marqs85/cps2_digiav/sw_common/sys_controller/src/menu.c

//
// Copyright (C) 2020  Markus Hiienkari <mhiienka@niksula.hut.fi>
//
// This file is part of CPS2 Digital AV Interface project.
//
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

#include <string.h>
#include "sysconfig.h"
#include "menu.h"
#include "avconfig.h"
#include "osd_generator_regs.h"
#include "controls.h"
#include "userdata.h"

#define MAX_MENU_DEPTH 1

#define OPT_NOWRAP  0
#define OPT_WRAP    1

#ifdef OSDLANG_JP
#define LNG(e, j) j
#else
#define LNG(e, j) e
#endif

#define FW_VER      "0.94"

extern avconfig_t tc;
extern volatile osd_regs *osd;

char menu_row1[OSD_CHAR_COLS+1];
char menu_row2[OSD_CHAR_COLS+1];

uint8_t menu_active;

menunavi navi[MAX_MENU_DEPTH];
uint8_t navlvl;

static const char *off_on_desc[] = { LNG("Off","ｵﾌ"), LNG("On","ｵﾝ") };
static const char *ad_mode_id_desc[] = { "240p_CRT", "480p_CRT (Line2x)", "1280x720 (Line3x)", "1280x1024 (Line4x)", "1920x1080 (Line4x)", "1920x1080 (Line5x)", "1600x1200 (Line5x)", "1920x1200 (Line5x)", "1920x1440 (Line6x)" };
static const char *tx_mode_desc[] = { "HDMI (RGB Full)", "HDMI (RGB Limited)", "HDMI (YCbCr444)", "DVI" };
static const char *sl_mode_desc[] = { "Off", "Horizontal", "H+V" };
static const char *sl_method_desc[] = { "Multiplication", "Subtraction" };
static const char *audio_sr_desc[] = { "Off", "On (4.0)", "On (5.1)", "On (7.1)" };
static const char *neogeo_freq_desc[] = { "24MHz (MVS)", "24.167MHz (AES)", "24.306MHz (DFO)" };

static void value_disp(uint8_t v) { if (v < 10) {menu_row2[0] = ('0'+v); menu_row2[1] = 0;} else {menu_row2[0] = '0'+(v/10); menu_row2[1] = '0'+(v%10); menu_row2[2] = 0;} }


MENU(menu_main, P99_PROTECT({ \
    { "Output mode",                            OPT_AVCONFIG_SELECTION, { .sel = { &tc.ad_mode_id,              OPT_WRAP, SETTING_ITEM(ad_mode_id_desc) } } },
    { "1080p L5x Y-offset",                     OPT_AVCONFIG_NUMVALUE,  { .num = { &tc.l5x_1080p_y_offset,      OPT_WRAP, 0, L5X_1080P_YOFF_MAX, value_disp } } },
    { LNG("Scanlines","ｽｷｬﾝﾗｲﾝ"),                OPT_AVCONFIG_SELECTION, { .sel = { &tc.sl_mode,                OPT_WRAP,   SETTING_ITEM(sl_mode_desc) } } },
    { "Sl. method",                             OPT_AVCONFIG_SELECTION, { .sel = { &tc.sl_method,             OPT_WRAP,   SETTING_ITEM(sl_method_desc) } } },
    { LNG("Sl. strength","ｽｷｬﾝﾗｲﾝﾂﾖｻ"),          OPT_AVCONFIG_NUMVALUE,  { .num = { &tc.sl_str,                 OPT_WRAP, 0, SCANLINESTR_MAX, value_disp } } },
    { "HDR flag",                               OPT_AVCONFIG_SELECTION,  { .sel = { &tc.adv7513_cfg.hdr,      OPT_WRAP, SETTING_ITEM(off_on_desc) } } },
    { "VRR flag",                               OPT_AVCONFIG_SELECTION,  { .sel = { &tc.adv7513_cfg.vrr,      OPT_WRAP, SETTING_ITEM(off_on_desc) } } },
    { "Quad stereo",                            OPT_AVCONFIG_SELECTION,  { .sel = { &tc.adv7513_cfg.i2s_stereo_cfg, OPT_WRAP, SETTING_ITEM(audio_sr_desc) } } },
#ifdef NEOGEO
    { "XTAL freq",                             OPT_AVCONFIG_SELECTION,  { .sel = { &tc.neogeo_freq,            OPT_WRAP, SETTING_ITEM(neogeo_freq_desc) } } },
#endif
    { LNG("TX mode","TXﾓｰﾄﾞ"),                  OPT_AVCONFIG_SELECTION, { .sel = { &tc.adv7513_cfg.tx_mode,     OPT_WRAP, SETTING_ITEM(tx_mode_desc) } } },
    { "<Save settings>",                        OPT_FUNC_CALL,          { .fun = { save_settings, NULL } } },
    { LNG("<Reset settings>","<ｾｯﾃｲｵｼｮｷｶ    >"),  OPT_FUNC_CALL,          { .fun = { reset_target_avconfig, NULL } } },
    { "<Firmware info>",                        OPT_FUNC_CALL,          { .fun = { get_fw_info, NULL } } },
    { "<Exit menu>",                            OPT_FUNC_CALL,          { .fun = { exit_menu, NULL } } },
}))


int is_menu_active() {
    return !!menu_active;
}

void init_menu() {
    menu_active = 0;
    memset(navi, 0, sizeof(navi));
    navi[0].m = &menu_main;
    navlvl = 0;
}

int exit_menu() {
    menu_active = 0;
    osd->osd_config.menu_active = 0;

    return 0;
}

int save_settings() {
    return write_userdata(0);
}

int get_fw_info() {
    strncpy(menu_row2, "v" FW_VER " @ " __DATE__, OSD_CHAR_COLS);

    return 1;
}

void write_option_value(menuitem_t *item, int func_called, int retval)
{
    switch (item->type) {
        case OPT_AVCONFIG_SELECTION:
            strncpy(menu_row2, item->sel.setting_str[*(item->sel.data)], OSD_CHAR_COLS+1);
            break;
        case OPT_AVCONFIG_NUMVALUE:
            item->num.df(*(item->num.data));
            break;
        case OPT_FUNC_CALL:
            if (func_called) {
                if (retval <= 0)
                    strncpy(menu_row2, ((retval==0) ? "Done" : "Failed"), OSD_CHAR_COLS+1);
            } else if (item->fun.arg_info) {
                item->fun.arg_info->df(*item->fun.arg_info->data);
            } else {
                menu_row2[0] = 0;
            }
            break;
        default:
            break;
    }
}

void render_osd_page() {
    int i;
    menuitem_t *item;
    uint32_t row_mask[2] = {0, 0};

    for (i=0; i < navi[navlvl].m->num_items; i++) {
        item = &navi[navlvl].m->items[i];
        strncpy((char*)osd->osd_array.data[i][0], item->name, OSD_CHAR_COLS);
        row_mask[0] |= (1<<i);

        if ((item->type != OPT_SUBMENU) && (item->type != OPT_FUNC_CALL)) {
            write_option_value(item, 0, 0);
            strncpy((char*)osd->osd_array.data[i][1], menu_row2, OSD_CHAR_COLS);
            row_mask[1] |= (1<<i);
        }
    }

    osd->osd_sec_enable[0].mask = row_mask[0];
    osd->osd_sec_enable[1].mask = row_mask[1];
}

void display_menu(menucode_id code)
{
    menuitem_t *item;
    uint8_t *val, val_wrap, val_min, val_max;
    uint16_t *val_u16, val_u16_min, val_u16_max;
    int i, func_called = 0, retval = 0;

    item = &navi[navlvl].m->items[navi[navlvl].mp];

    // Parse menu control
    switch (code) {
    case SHOW_MENU:
        menu_active = 1;
        render_osd_page();
        osd->osd_config.menu_active = 1;
        break;
    case NEXT_OPT:
        if (item->type == OPT_FUNC_CALL)
            osd->osd_sec_enable[1].mask &= ~(1<<navi[navlvl].mp);
        navi[navlvl].mp = (navi[navlvl].mp+1) % navi[navlvl].m->num_items;
        break;
    case VAL_PLUS:
        switch (item->type) {
            case OPT_AVCONFIG_SELECTION:
            case OPT_AVCONFIG_NUMVALUE:
                val = item->sel.data;
                val_wrap = item->sel.wrap_cfg;
                val_min = item->sel.min;
                val_max = item->sel.max;
                *val = (*val < val_max) ? (*val+1) : (val_wrap ? val_min : val_max);
                break;
            case OPT_FUNC_CALL:
                retval = item->fun.f();
                func_called = 1;
                break;
            default:
                break;
        }
        break;
    default:
        break;
    }

    // Generate menu text
    item = &navi[navlvl].m->items[navi[navlvl].mp];
    strncpy(menu_row1, item->name, OSD_CHAR_COLS+1);
    write_option_value(item, func_called, retval);
    strncpy((char*)osd->osd_array.data[navi[navlvl].mp][1], menu_row2, OSD_CHAR_COLS);
    osd->osd_row_color.mask = (1<<navi[navlvl].mp);
    if (func_called || ((item->type == OPT_FUNC_CALL) && item->fun.arg_info != NULL))
        osd->osd_sec_enable[1].mask |= (1<<navi[navlvl].mp);
}
