marqs85/cps2_digiav/board/cps2/rtl/i2s_upsampler_2x.v

//
// Copyright (C) 2016-2017  Markus Hiienkari <mhiienka@niksula.hut.fi>
//
// This file is part of CPS2_digiav project.
//
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

`define I2S_CLK_GATING
`define DEBUG

module i2s_upsampler_2x (
    input reset_n,
    input I2S_BCK,
    input I2S_WS,
    input I2S_DATA,
    output I2S_BCK_out,
    output reg I2S_WS_out,
    output reg I2S_DATA_out,
    output reg [7:0] clkcnt_out
);

reg I2S_WS_2x;
reg I2S_DATA_2x;

reg I2S_WS_prev;
reg [2:0] sample_idx;
reg [2:0] resample_idx;

// Synchronizer regs
reg [2:0] sample_idx_L;
reg [2:0] sample_idx_LL;

// sample FIFO and pointers
reg [15:0] samplebuf_l[0:3];
reg [15:0] samplebuf_r[0:3];
reg [4:0] samplebuf_l_ctr;
reg [4:0] samplebuf_r_ctr;

reg [9:0] sample2x_ctr;
reg [4:0] resample_l_ctr;
reg [4:0] resample_r_ctr;

reg [7:0] clkcnt;
reg [5:0] clken_ctr;
reg clken;

`ifdef DEBUG
reg [7:0] bck_ctr;
reg [6:0] frame_ctr;

reg dbg_len_exp /* synthesis noprune */;
reg dbg_frame_exp /* synthesis noprune */;

reg dbg_fifo_ovf /* synthesis noprune */;
reg dbg_fifo_unf /* synthesis noprune */;
`endif

wire I2S_BCK_proc;

// I2S_BCK_out = (4/5)*I2S_BCK = 4MHz
pll_i2s pll_i2s_inst (
    .inclk0(I2S_BCK),
    .c0(I2S_BCK_proc),
    .locked()
);


// Record 16-bit samples at their native rate on the FIFO.
// Nominal CPS2 WS timing: 208 BCK cycles (31/32 frames), 192 BCK cycles (1/32 frames) -> avg: 207.5 BCK cycles.
// However, jitter in WS timing may occur due to e.g. insufficient PSU (check dbg_len_exp in SignalTap).
always @(posedge I2S_BCK or negedge reset_n)
begin
    if (!reset_n) begin
        samplebuf_l_ctr <= 0;
        samplebuf_r_ctr <= 0;
        I2S_WS_prev <= 0;
        sample_idx <= 0;
        clkcnt <= 0;
    end else begin
        if ((I2S_WS_prev == 1'b1) && (I2S_WS == 1'b0)) begin
            samplebuf_l_ctr <= 16;
            clkcnt_out <= clkcnt;
            sample_idx <= sample_idx + 1'b1;
        end else if ((I2S_WS_prev == 1'b0) && (I2S_WS == 1'b1)) begin
            samplebuf_r_ctr <= 16;
        end

        if (samplebuf_l_ctr > 0) begin
            samplebuf_l[sample_idx][samplebuf_l_ctr-1] <= I2S_DATA;
            samplebuf_l_ctr <= samplebuf_l_ctr - 1;
        end

        if (samplebuf_r_ctr > 0) begin
            samplebuf_r[sample_idx][samplebuf_r_ctr-1] <= I2S_DATA;
            samplebuf_r_ctr <= samplebuf_r_ctr - 1;
        end

        if ((I2S_WS_prev == 1'b1) && (I2S_WS == 1'b0))
            clkcnt <= 0;
        else
            clkcnt <= clkcnt + 1'b1;

        I2S_WS_prev <= I2S_WS;

`ifdef DEBUG
        if ((I2S_WS_prev == 1'b1) && (I2S_WS == 1'b0)) begin
            if (bck_ctr == 207) begin
                frame_ctr <= frame_ctr + 1;
            end else if (bck_ctr == 191) begin
                if (frame_ctr != 31)
                    dbg_frame_exp <= 1;

                frame_ctr <= 0;
            end else begin
                dbg_len_exp <= 1;
                if (bck_ctr < 200)
                    frame_ctr <= 0;
                else
                    frame_ctr <= frame_ctr + 1;
            end
            
            bck_ctr <= 0;
        end else begin
            bck_ctr <= bck_ctr + 1;
            dbg_len_exp <= 0;
            dbg_frame_exp <= 0;
        end
`endif
    end
end

initial begin
    resample_idx = 3'd4;
end

// Output samples at 2x rate (~48kHz), 83 o_BCK cycles per o_WS cycle.
always @(posedge I2S_BCK_proc or negedge reset_n)
begin
    reg [3:0] sample_idx_norm;

    if (!reset_n) begin
        sample2x_ctr <= 0;
        resample_l_ctr <= 0;
        resample_r_ctr <= 0;
        resample_idx <= 3'd4;
        clken_ctr <= 0;
    end else begin
        if ((sample2x_ctr == 0) || (sample2x_ctr == 83)) begin
            I2S_WS_2x <= 1'b0;
            resample_l_ctr <= 16;
            clken_ctr <= 32;
        end else if ((sample2x_ctr == 42) || (sample2x_ctr == (42+83))) begin
            I2S_WS_2x <= 1'b1;
            resample_r_ctr <= 16;
            clken_ctr <= 32;
        end else begin
            if (clken_ctr > 0)
                clken_ctr <= clken_ctr - 1'b1;
        end

        if (sample_idx_LL < resample_idx)
            sample_idx_norm = 4'd8 + sample_idx_LL;
        else
            sample_idx_norm = sample_idx_LL;

        if (sample2x_ctr == (83*2-1)) begin
            sample2x_ctr <= 0;

            // Check if FIFO is going to over/underflow
            if (sample_idx_norm > resample_idx + 4'd6) begin
                resample_idx <= resample_idx + 3;
`ifdef DEBUG
                dbg_fifo_unf <= 1'b1;
`endif
            end else if (sample_idx_norm < resample_idx + 4'd2) begin
                resample_idx <= resample_idx - 1;
`ifdef DEBUG
                dbg_fifo_ovf <= 1'b1;
`endif
            end else begin
                resample_idx <= resample_idx + 1'b1;
`ifdef DEBUG
                dbg_fifo_ovf <= 0;
                dbg_fifo_unf <= 0;
`endif
            end
        end else begin
            sample2x_ctr <= sample2x_ctr + 1'b1;
        end

        if (resample_l_ctr > 0) begin
            I2S_DATA_2x <= samplebuf_l[resample_idx][resample_l_ctr-1];
            resample_l_ctr <= resample_l_ctr - 1;
        end else if (resample_r_ctr > 0) begin
            I2S_DATA_2x <= samplebuf_r[resample_idx][resample_r_ctr-1];
            resample_r_ctr <= resample_r_ctr - 1;
        end

        sample_idx_L <= sample_idx;
        sample_idx_LL <= sample_idx_L;
    end
end

// launch outputs ar negative edge
always @(negedge I2S_BCK_proc)
begin
    I2S_WS_out <= I2S_WS_2x;
    I2S_DATA_out <= I2S_DATA_2x;
end

`ifdef I2S_CLK_GATING
always @(negedge I2S_BCK_proc)
begin
    clken <= (clken_ctr > 0) ? 1'b1 : 1'b0;
end

assign I2S_BCK_out = (I2S_BCK_proc & clken);
`else
assign I2S_BCK_out = I2S_BCK_proc;
`endif

endmodule
