marqs85/cps2_digiav/sw_common/sys_controller/inc/video_modes.h

//
// Copyright (C) 2020  Markus Hiienkari <mhiienka@niksula.hut.fi>
//
// This file is part of CPS2 Digital AV Interface project.
//
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

#ifndef VIDEO_MODES_H_
#define VIDEO_MODES_H_

#include <stdint.h>
#include "si5351.h"
#include "adv7513.h"

typedef enum {
    CRTMODE_240p      = 0,
    STDMODE_240p      = 1,
    CRTMODE_480p      = 2,
    STDMODE_480p      = 3,
    STDMODE_720p      = 5,
    STDMODE_1280x960  = 6,
    STDMODE_1280x1024 = 7,
    STDMODE_1080p     = 8,
    STDMODE_1600x1200 = 9,
    STDMODE_1920x1200 = 10,
    STDMODE_1920x1440 = 11
} mode_idx_t;

typedef enum {
    ADMODE_240p_CRT  = 0,
    ADMODE_480p_CRT  = 1,
    ADMODE_720p      = 2,
    ADMODE_1280x1024 = 3,
    ADMODE_1080p_4X  = 4,
    ADMODE_1080p_5X  = 5,
    ADMODE_1600x1200 = 6,
    ADMODE_1920x1200 = 7,
    ADMODE_1920x1440 = 8,
    ADMODE_LAST      = 8
} ad_mode_id_t;

typedef struct {
    uint16_t h_active;
    uint16_t v_active;
    uint16_t h_total;
    uint8_t  h_total_adj:5;
    uint16_t v_total:11;
    uint16_t h_backporch:9;
    uint16_t v_backporch:9;
    uint16_t h_synclen:9;
    uint8_t v_synclen:5;
} __attribute__((packed)) sync_timings_t;

typedef struct {
    uint32_t c1_hz;
    uint32_t vclks_per_frame;
    sync_timings_t timings;
    si5351_ms_config_t vclk_to_mclk_conf;
} source_params_t;

typedef struct {
    char name[10];
    HDMI_vic_t vic:8;
    sync_timings_t timings;
    HDMI_pixelrep_t tx_pixelrep:2;
    HDMI_pixelrep_t hdmitx_pixr_ifr:2;
    // for generated target mode
    uint8_t si_pclk_mult:4;
    si5351_ms_config_t si_ms_conf;
} mode_data_t;

typedef struct {
    ad_mode_id_t id;
    const source_params_t *src_params;
    uint8_t x_rpt;
    uint8_t y_rpt;
    int16_t x_offset_i;
    int16_t y_offset_i;
    si5351_ms_config_t si_ms_conf;
} ad_mode_data_t;

typedef struct {
    uint8_t x_rpt;
    uint8_t y_rpt;
    uint8_t x_skip;
    int16_t x_offset;
    int16_t y_offset;
    uint16_t x_size;
    uint16_t y_size;
    uint16_t framesync_line;
    uint8_t x_start_lb;
    int8_t y_start_lb;
} vm_mult_config_t;

typedef struct {
    uint16_t h_active;
    uint16_t v_active;
    uint32_t vclks_per_frame;
} input_mode_t;


void set_default_vm_table();

void step_ad_mode(uint8_t next);

uint32_t estimate_dotclk(mode_data_t *vm_in, uint32_t h_hz);

const ad_mode_data_t* get_output_mode(input_mode_t *im, ad_mode_id_t ad_mode_id, vm_mult_config_t *vm_conf, mode_data_t *vm_in, mode_data_t *vm_out);

#endif /* VIDEO_MODES_H_ */
