marqs85/cps2_digiav/sw_common/sys_controller/inc/menu.h

//
// Copyright (C) 2020  Markus Hiienkari <mhiienka@niksula.hut.fi>
//
// This file is part of CPS2 Digital AV Interface project.
//
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

#ifndef MENU_H_
#define MENU_H_

#include <stdint.h>

typedef enum {
    OPT_AVCONFIG_SELECTION,
    OPT_AVCONFIG_NUMVALUE,
    OPT_AVCONFIG_NUMVAL_U16,
    OPT_SUBMENU,
    OPT_FUNC_CALL,
} menuitem_type;

typedef int (*func_call)(void);
typedef void (*arg_func)(void);
typedef void (*disp_func)(uint8_t);
typedef void (*disp_func_u16)(uint16_t*);

typedef struct {
    uint8_t *data;
    uint8_t max;
    disp_func df;
} arg_info_t;

typedef struct {
    uint8_t *data;
    uint8_t wrap_cfg;
    uint8_t min;
    uint8_t max;
    const char **setting_str;
} opt_avconfig_selection;

typedef struct {
    uint8_t *data;
    uint8_t wrap_cfg;
    uint8_t min;
    uint8_t max;
    disp_func df;
} opt_avconfig_numvalue;

typedef struct {
    uint16_t *data;
    uint16_t min;
    uint16_t max;
    disp_func_u16 df;
} opt_avconfig_numvalue_u16;

typedef struct {
    func_call f;
    const arg_info_t *arg_info;
} opt_func_call;

typedef struct menustruct menu_t;

typedef struct {
    const menu_t *menu;
    const arg_info_t *arg_info;
    arg_func arg_f;
} opt_submenu;

typedef struct {
    const char *name;
    menuitem_type type;
    union {
        opt_avconfig_selection sel;
        opt_avconfig_numvalue num;
        opt_avconfig_numvalue_u16 num_u16;
        opt_submenu sub;
        opt_func_call fun;
    };
} menuitem_t;

struct menustruct {
    uint8_t num_items;
    menuitem_t *items;
};

#define SETTING_ITEM(x) 0, sizeof(x)/sizeof(char*)-1, x
#define MENU(X, Y) menuitem_t X##_items[] = Y; const menu_t X = { sizeof(X##_items)/sizeof(menuitem_t), X##_items };
#define P99_PROTECT(...) __VA_ARGS__

typedef enum {
    SHOW_MENU    = 0,
    NEXT_OPT,
    VAL_PLUS
} menucode_id;

typedef struct {
    const menu_t *m;
    uint8_t mp;
} menunavi;

int is_menu_active();
void init_menu();
int exit_menu();
int save_settings();
int get_fw_info();
void render_osd_page();
void display_menu(menucode_id code);

#endif
